deeptoaster/nato-lights/src/pattern.h

#pragma once

class Pattern {
 public:
  virtual void init() {}
  virtual unsigned char step() {}
  virtual ~Pattern() {}
};

class Factory {
 public:
  virtual Pattern *getInstance() = 0;
  Factory *next;
  Factory *previous;
};

template<class TPattern>
class PatternFactory : Factory {
  Pattern *getInstance();
  Factory *next;
  Factory *previous;
};

template<class TPattern>
Pattern *PatternFactory<TPattern>::getInstance() {
  return new TPattern();
}
