deeptoaster/nato-lights/src/common.h

#include <FastLED.h>

#include "hardware.h"
#include "../config.h"

#define LED_COUNT_MAX (LED_COUNT_1 >= LED_COUNT_2 && LED_COUNT >= LED_COUNT_3 ? LED_COUNT_1 : LED_COUNT_2 >= LED_COUNT_3 ? LED_COUNT_2 : LED_COUNT_3)
#define LED_COUNT (LED_COUNT_1 + LED_COUNT_2 + LED_COUNT_3)
#define LED_BUFFER_PADDING (LED_COUNT_MAX * (LED_DUPLICATION - 1))
#define LED_BUFFER_SIZE (LED_COUNT + LED_BUFFER_PADDING)
#define LED_OFFSET_1 0
#define LED_OFFSET_2 (LED_OFFSET_1 + LED_COUNT_1)
#define LED_OFFSET_3 (LED_OFFSET_2 + LED_COUNT_2)

extern CRGB leds[LED_BUFFER_SIZE];
extern HardwareControl Hardware;
